Shedatheds/ModularHydroponicTowerGarden/images/8.jpg

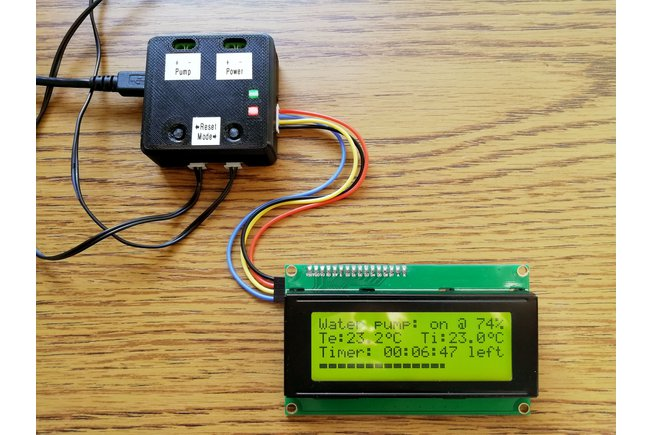
images/8.jpg
