Shedatheds/ModularHydroponicTowerGarden/3DPrint/STEP/Lid_Without_Holes.STEP

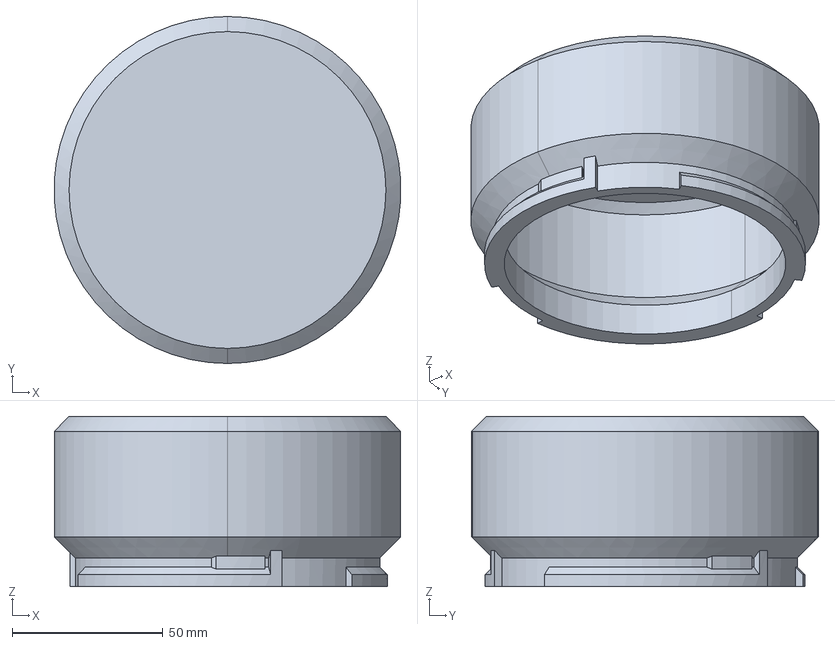
[picture p22: CAD file, 2025-03-30]
3DPrint/STEP/Lid_Without_Holes.STEP
114.8 x 115.0 x 56.5 mm
