Shedatheds/ModularHydroponicTowerGarden/3DPrint/STEP/Jiffy-7_41_Pot_02.STEP

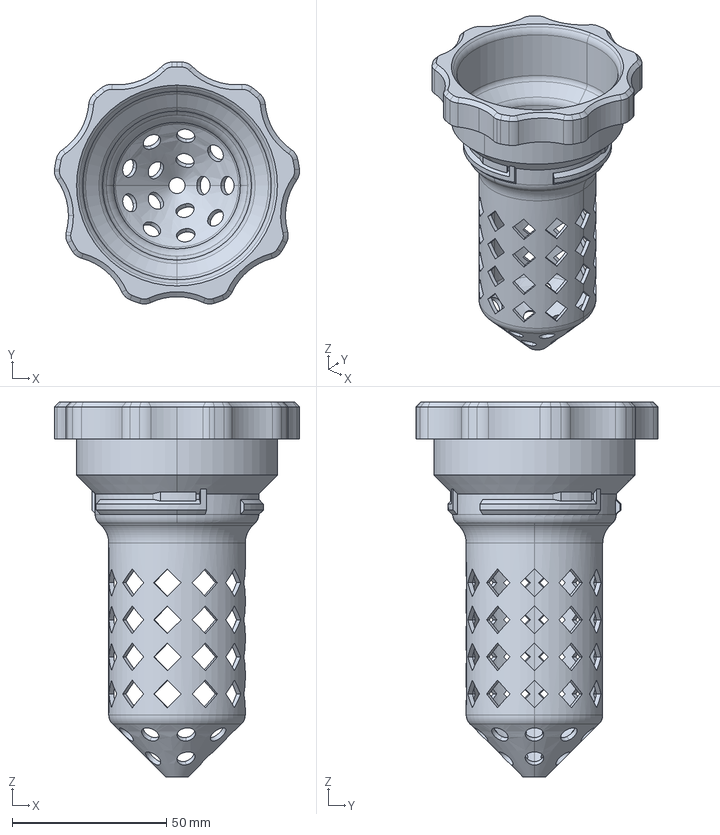
[picture p23: CAD file, 2025-03-30]
3DPrint/STEP/Jiffy-7_41_Pot_02.STEP
79.4 x 78.4 x 121.4 mm
