Shedatheds/ModularHydroponicTowerGarden/3DPrint/STEP/5-Way_Planting_Module_Hollow_Without_M3.STEP

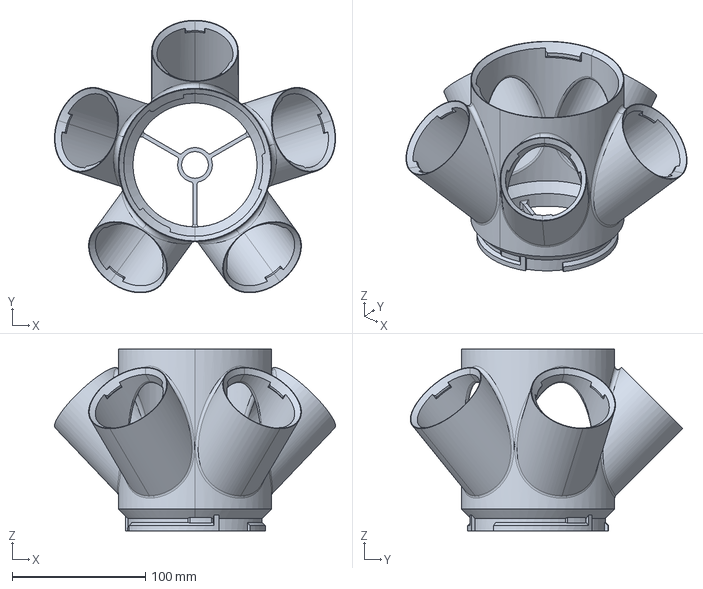
[picture p24: CAD file, 2025-03-30]
3DPrint/STEP/5-Way_Planting_Module_Hollow_Without_M3.STEP
210.8 x 204.4 x 136.5 mm
