Shedatheds/ModularHydroponicTowerGarden/3DPrint/STEP/Module_Spacer_80mm.STEP

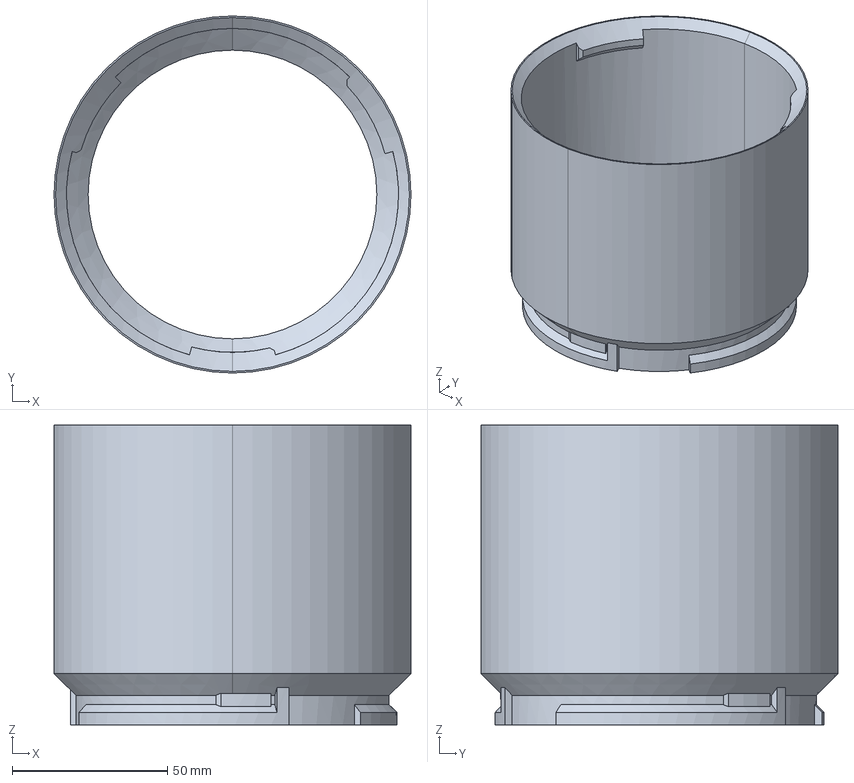
[picture p25: CAD file, 2025-03-30]
3DPrint/STEP/Module_Spacer_80mm.STEP
115.0 x 115.0 x 96.5 mm
