Shedatheds/ModularHydroponicTowerGarden/3DPrint/STEP/Dispenser_Module_External_01_Without_Holes.STEP

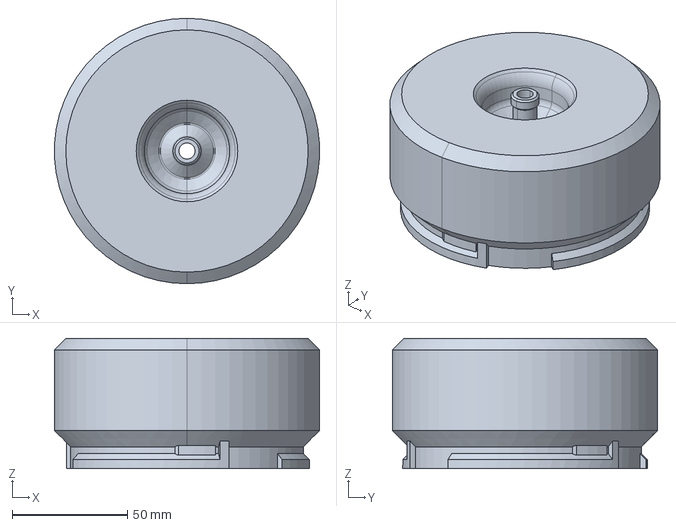
[picture p26: CAD file, 2025-03-30]
3DPrint/STEP/Dispenser_Module_External_01_Without_Holes.STEP
114.8 x 115.0 x 56.5 mm
