Shedatheds/ModularHydroponicTowerGarden/3DPrint/STEP/Waterpump_Hose_Adapter.STEP

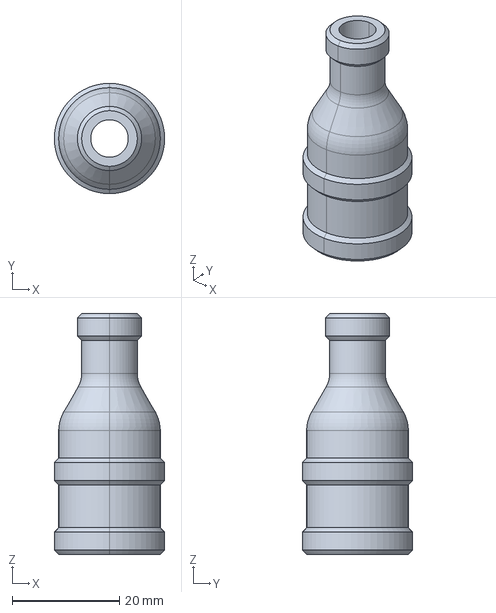
[picture p27: CAD file, 2025-03-30]
3DPrint/STEP/Waterpump_Hose_Adapter.STEP
20.6 x 20.6 x 45.0 mm
