Shedatheds/ModularHydroponicTowerGarden/3DPrint/STEP/2-Way_Planting_Module_Hollow_Without_M3.STEP

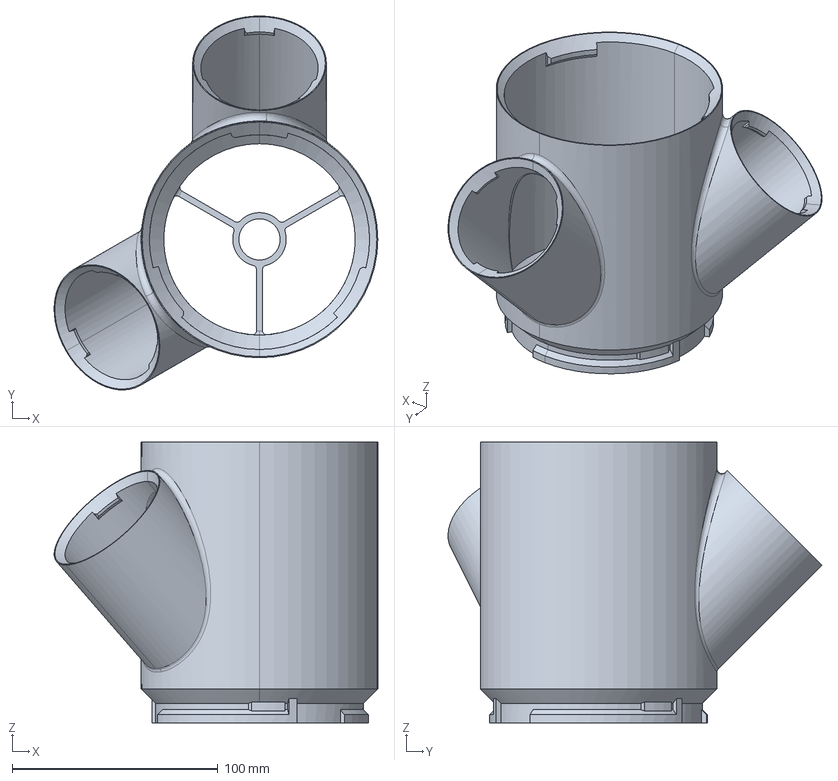
[picture p28: CAD file, 2025-03-30]
3DPrint/STEP/2-Way_Planting_Module_Hollow_Without_M3.STEP
157.3 x 181.7 x 136.5 mm
