Shedatheds/ModularHydroponicTowerGarden/3DPrint/STEP/Module_Spacer_40mm.STEP

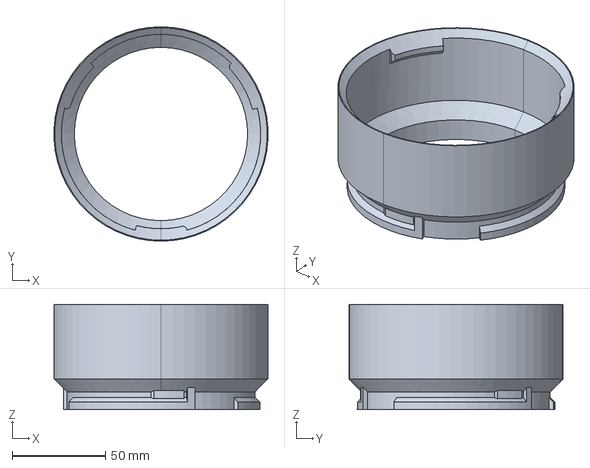
[picture p29: CAD file, 2025-03-30]
3DPrint/STEP/Module_Spacer_40mm.STEP
114.8 x 115.0 x 56.5 mm
