Shedatheds/ModularHydroponicTowerGarden/3DPrint/STEP/Standard_Pot_Raw.STEP

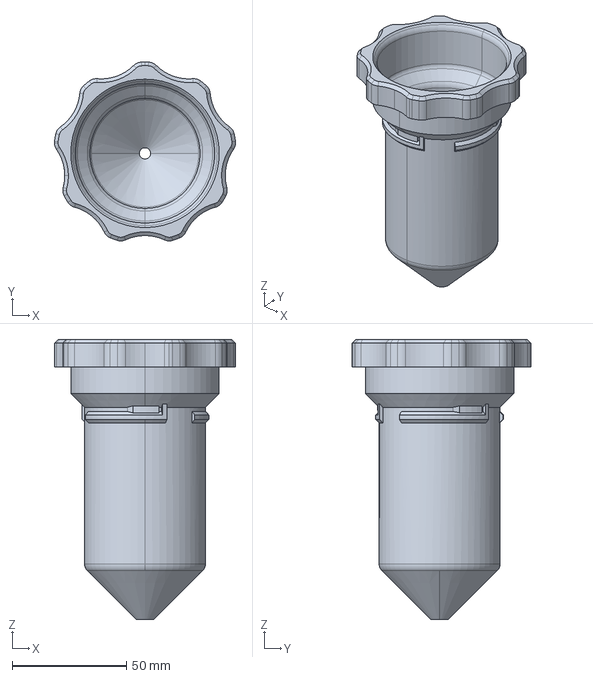
[picture p30: CAD file, 2025-03-30]
3DPrint/STEP/Standard_Pot_Raw.STEP
79.4 x 78.4 x 122.6 mm
