Shedatheds/ModularHydroponicTowerGarden/3DPrint/STEP/4-Way_Planting_Module_Hollow.STEP

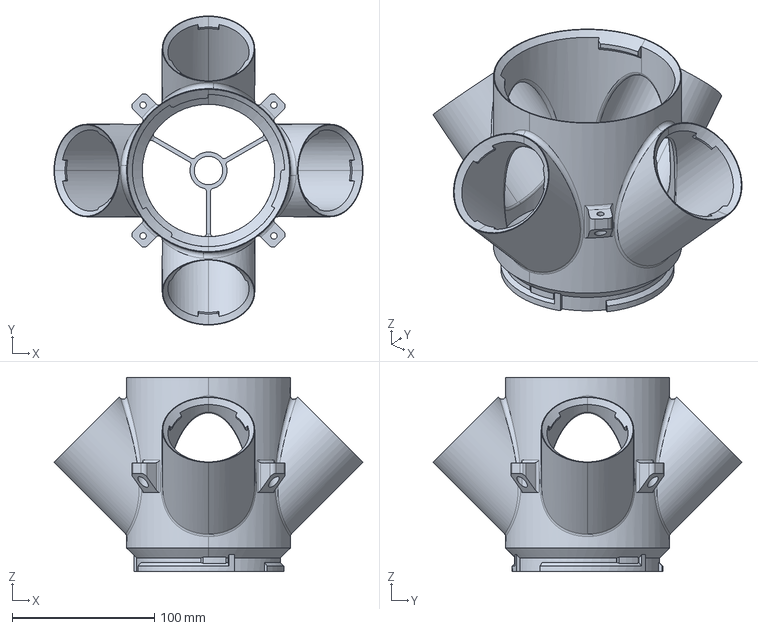
[picture p31: CAD file, 2025-03-30]
3DPrint/STEP/4-Way_Planting_Module_Hollow.STEP
217.1 x 217.1 x 136.5 mm
