Shedatheds/ModularHydroponicTowerGarden/3DPrint/STEP/3-Way_Planting_Module.STEP

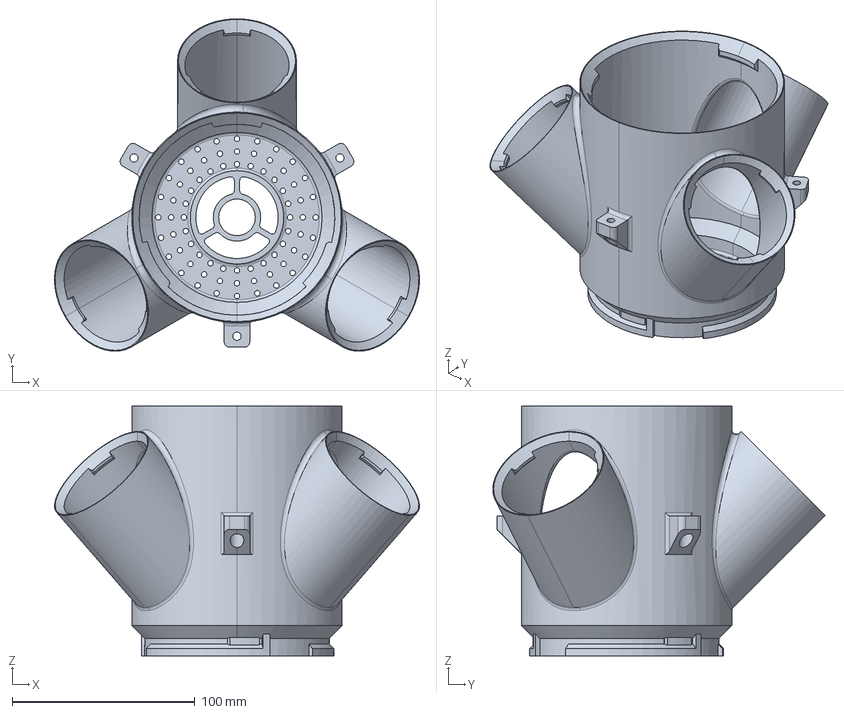
[picture p32: CAD file, 2025-03-30]
3DPrint/STEP/3-Way_Planting_Module.STEP
199.5 x 181.7 x 136.5 mm
