Shedatheds/ModularHydroponicTowerGarden/3DPrint/STEP/Jiffy-7_41_Pot_For_4-5-Way_Planting_Module.STEP

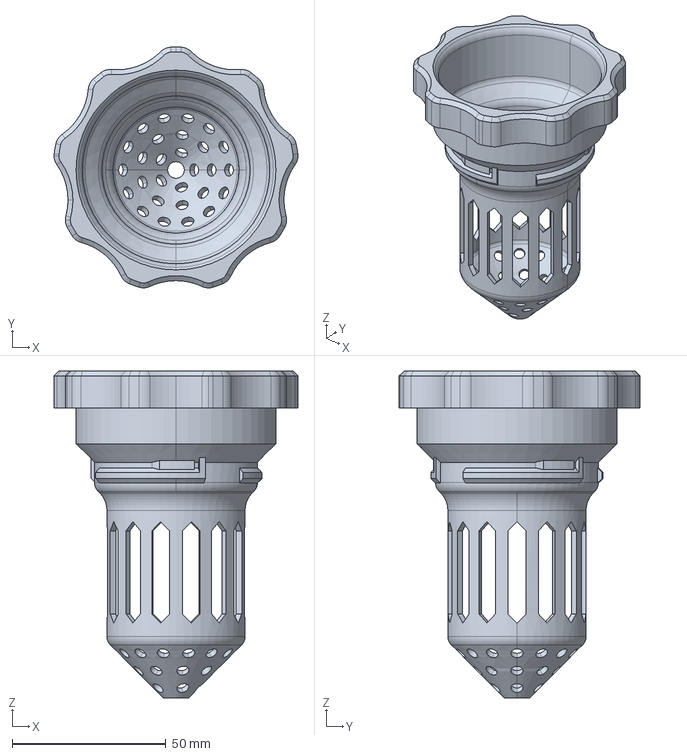
[picture p33: CAD file, 2025-03-30]
3DPrint/STEP/Jiffy-7_41_Pot_For_4-5-Way_Planting_Module.STEP
79.4 x 78.4 x 106.4 mm
