Shedatheds/ModularHydroponicTowerGarden/3DPrint/STEP/Pot_Adapter.STEP

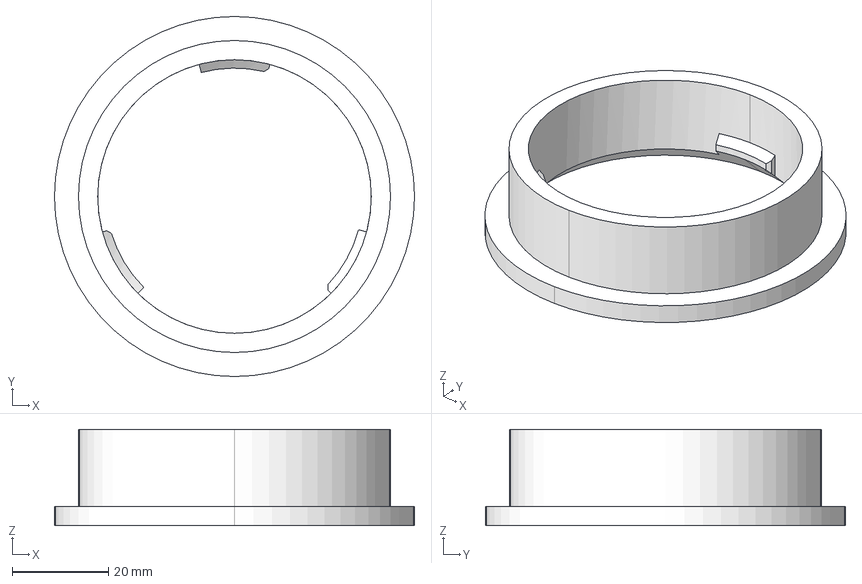
[picture p34: CAD file, 2025-03-30]
3DPrint/STEP/Pot_Adapter.STEP
75.0 x 75.0 x 20.0 mm
