Shedatheds/ModularHydroponicTowerGarden/3DPrint/STEP/Module_Adapter_02.STEP

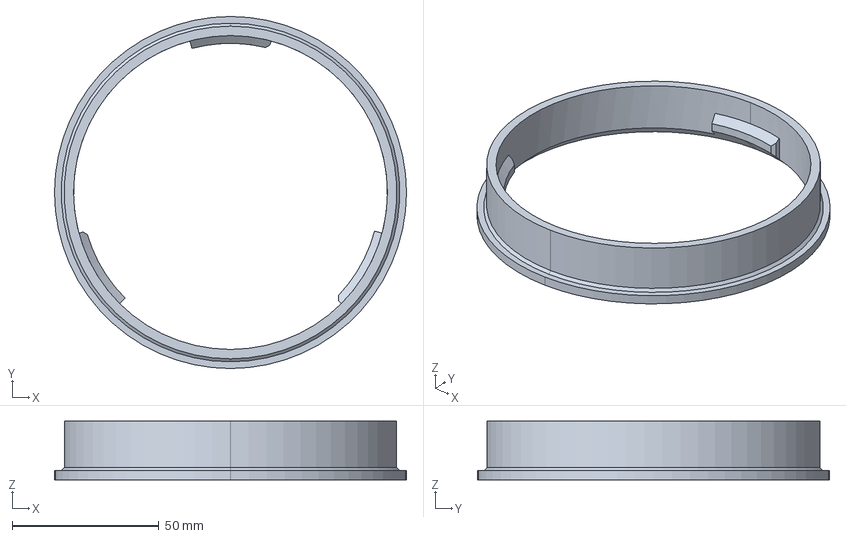
[picture p35: CAD file, 2025-03-30]
3DPrint/STEP/Module_Adapter_02.STEP
120.0 x 120.0 x 20.0 mm
