Shedatheds/ModularHydroponicTowerGarden/3DPrint/STEP/1-Way_Planting_Module_Hollow_Without_M3.STEP

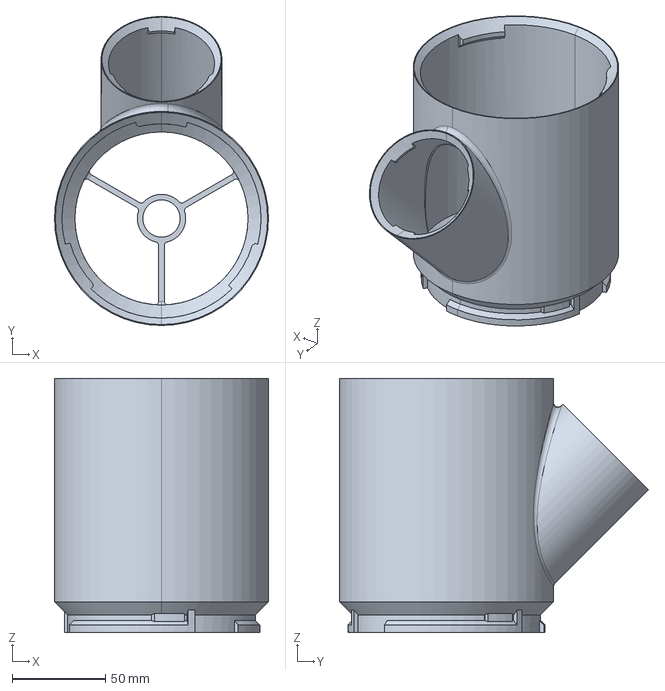
[picture p36: CAD file, 2025-03-30]
3DPrint/STEP/1-Way_Planting_Module_Hollow_Without_M3.STEP
115.0 x 166.0 x 136.5 mm
