Shedatheds/ModularHydroponicTowerGarden/3DPrint/STEP/Filling_Module_mod_01.STEP

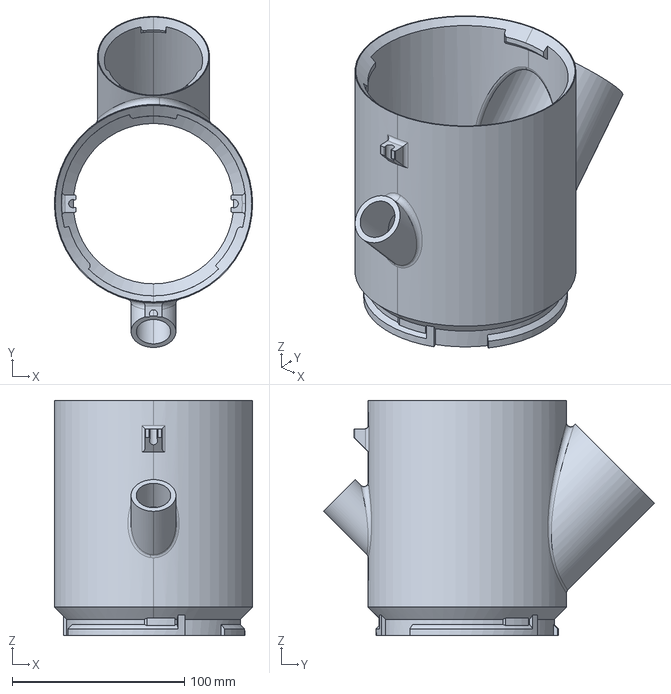
[picture p37: CAD file, 2025-03-30]
3DPrint/STEP/Filling_Module_mod_01.STEP
115.0 x 192.0 x 136.5 mm
