Shedatheds/ModularHydroponicTowerGarden/3DPrint/STEP/OESTLIG_Plant_Pot_12_12_Adapter.STEP

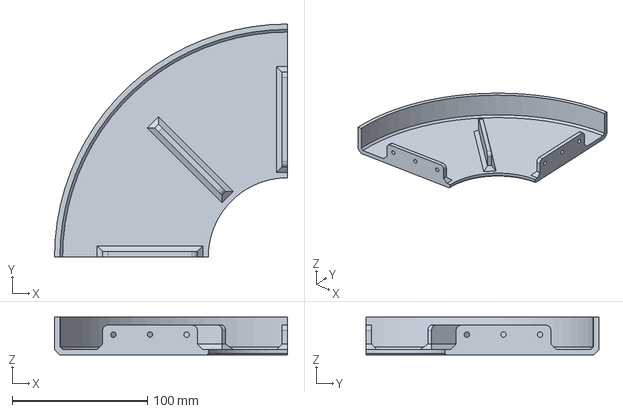
[picture p38: CAD file, 2025-03-30]
3DPrint/STEP/OESTLIG_Plant_Pot_12_12_Adapter.STEP
172.0 x 172.0 x 28.0 mm
