Shedatheds/ModularHydroponicTowerGarden/3DPrint/STEP/Filtration_Mesh_Holder_01.STEP

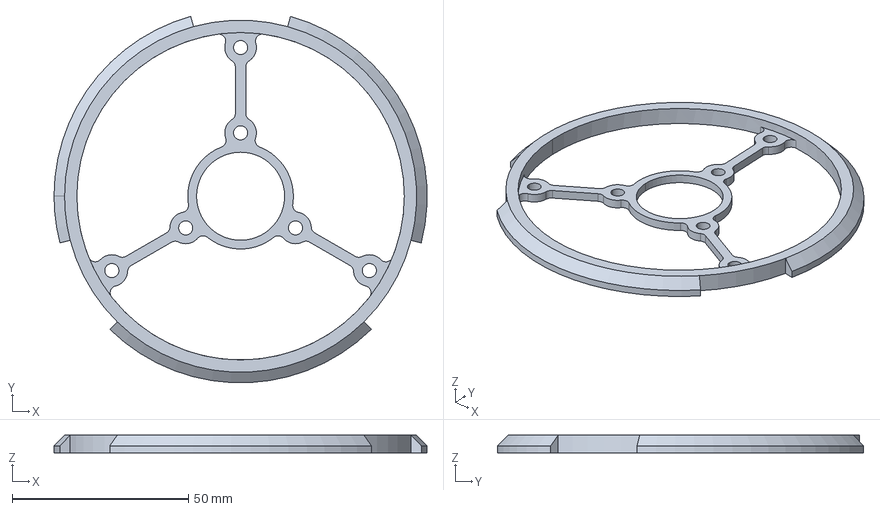
[picture p39: CAD file, 2025-03-30]
3DPrint/STEP/Filtration_Mesh_Holder_01.STEP
105.9 x 104.0 x 5.00 mm
