Shedatheds/ModularHydroponicTowerGarden/3DPrint/STEP/Jiffy-7_41_Pot.STEP

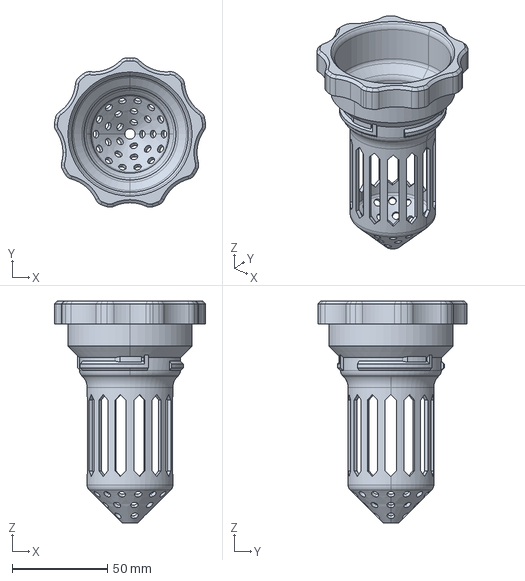
[picture p41: CAD file, 2025-03-30]
3DPrint/STEP/Jiffy-7_41_Pot.STEP
79.4 x 78.4 x 116.4 mm
