Shedatheds/ModularHydroponicTowerGarden/3DPrint/STEP/Dispenser_Module_Internal.STEP

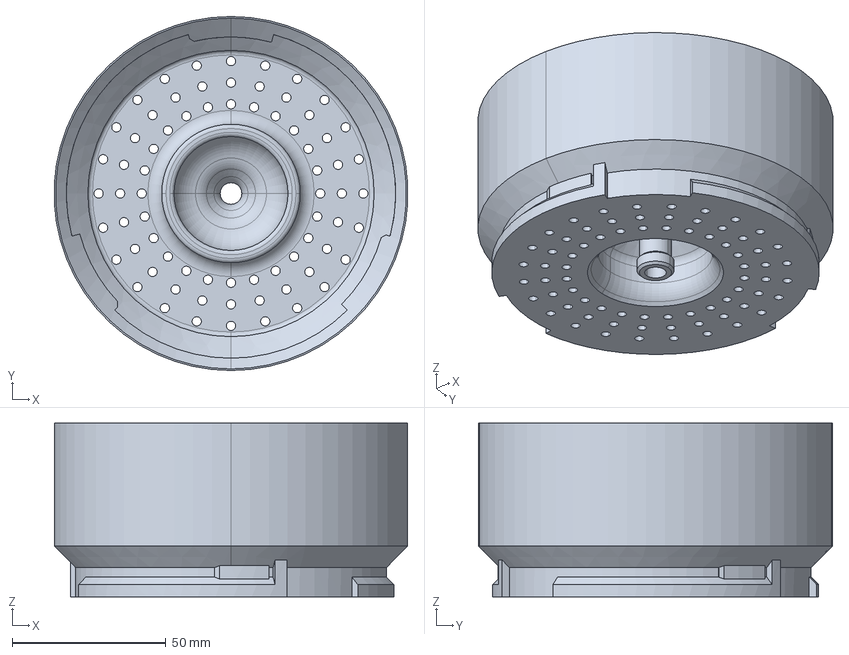
[picture p42: CAD file, 2025-03-30]
3DPrint/STEP/Dispenser_Module_Internal.STEP
114.8 x 115.0 x 56.5 mm
