Shedatheds/ModularHydroponicTowerGarden/3DPrint/STEP/OESTLIG_Plant_Pot_14_12x14_12_Adapter.STEP

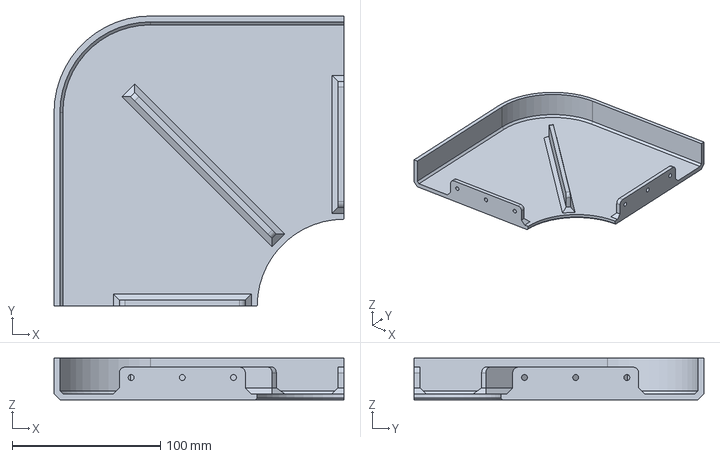
[picture p43: CAD file, 2025-03-30]
3DPrint/STEP/OESTLIG_Plant_Pot_14_12x14_12_Adapter.STEP
195.5 x 195.5 x 28.0 mm
