Shedatheds/ModularHydroponicTowerGarden/3DPrint/STEP/Standard_Pot_02.STEP

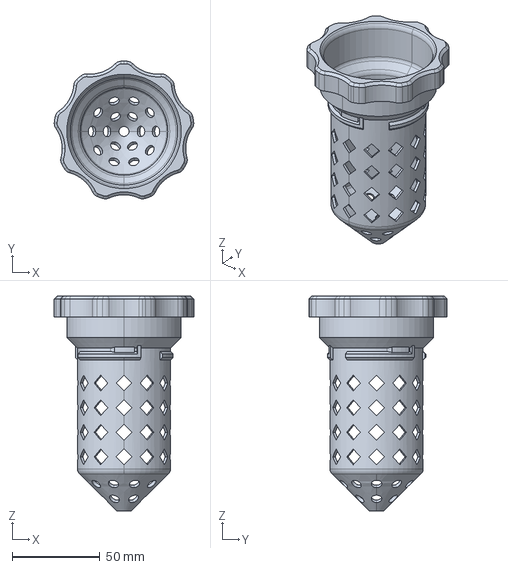
[picture p45: CAD file, 2025-03-30]
3DPrint/STEP/Standard_Pot_02.STEP
79.4 x 78.4 x 122.3 mm
