Shedatheds/ModularHydroponicTowerGarden/3DPrint/STEP/1-Way_Planting_Module.STEP

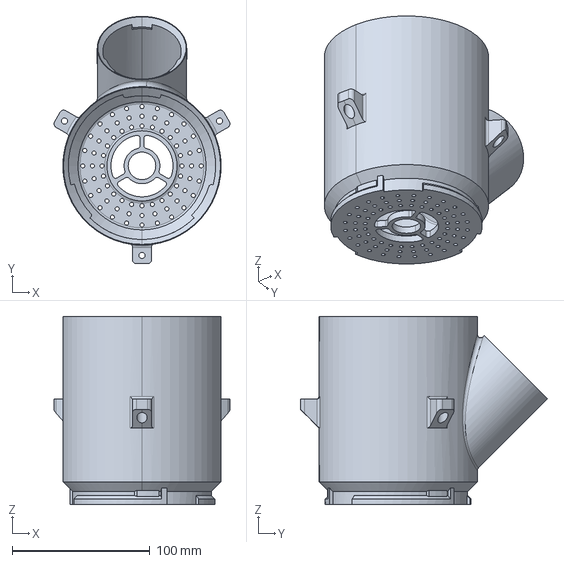
[picture p48: CAD file, 2025-03-30]
3DPrint/STEP/1-Way_Planting_Module.STEP
127.8 x 179.5 x 136.5 mm
