Shedatheds/ModularHydroponicTowerGarden/3DPrint/STEP/2-Way_Planting_Module.STEP

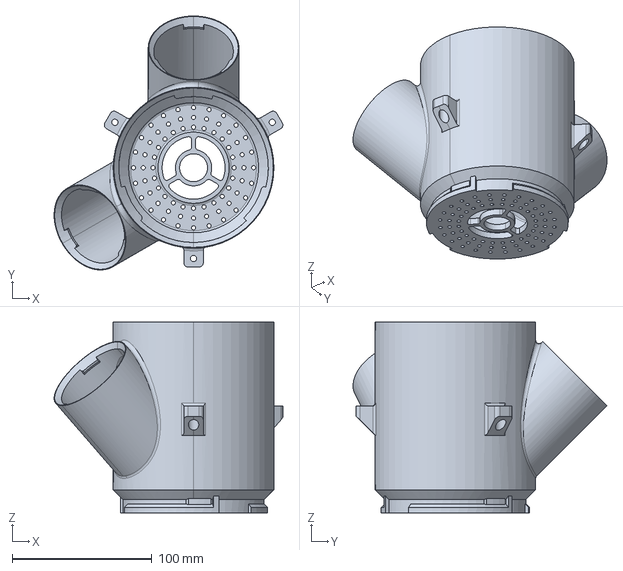
[picture p49: CAD file, 2025-03-30]
3DPrint/STEP/2-Way_Planting_Module.STEP
163.7 x 181.7 x 136.5 mm
